holmesrichards/precadsr/Images/PXL_20210831_000949090.jpg

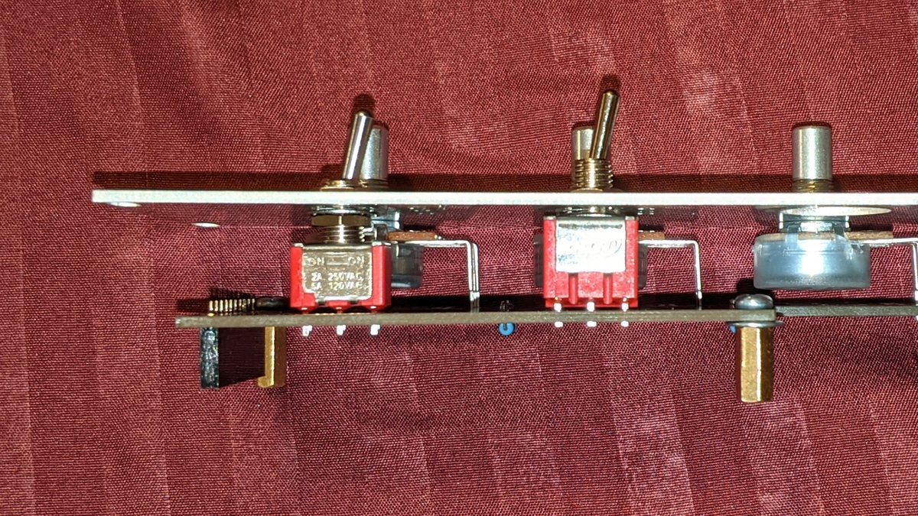
Images/PXL_20210831_000949090.jpg
