holmesrichards/precadsr/Images/PXL_20210831_002553634.jpg

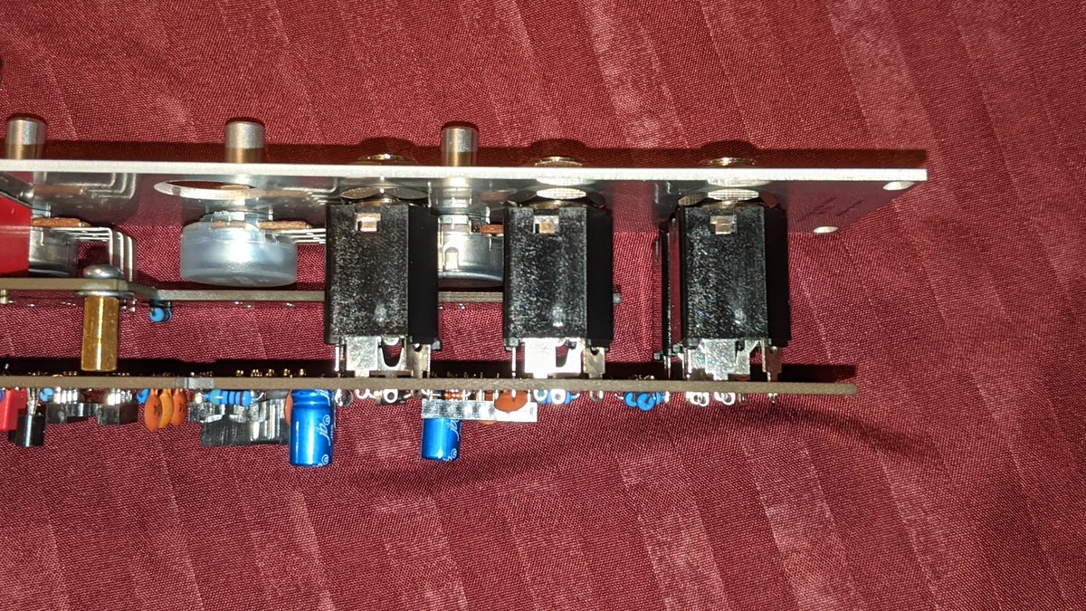
Images/PXL_20210831_002553634.jpg
